sq6emm/SR6LB/3dprints/beacon-10ghz-case-mount.FCStd

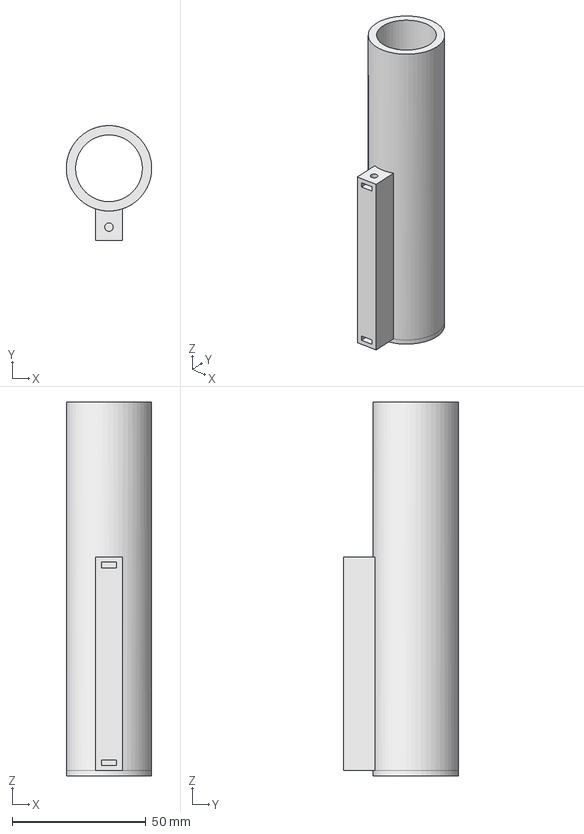
[picture p13: CAD file, 2025-03-09]
3dprints/beacon-10ghz-case-mount.FCStd
32.0 x 43.0 x 140.0 mm
