sq6emm/SR6LB/3dprints/beacon-case.FCStd

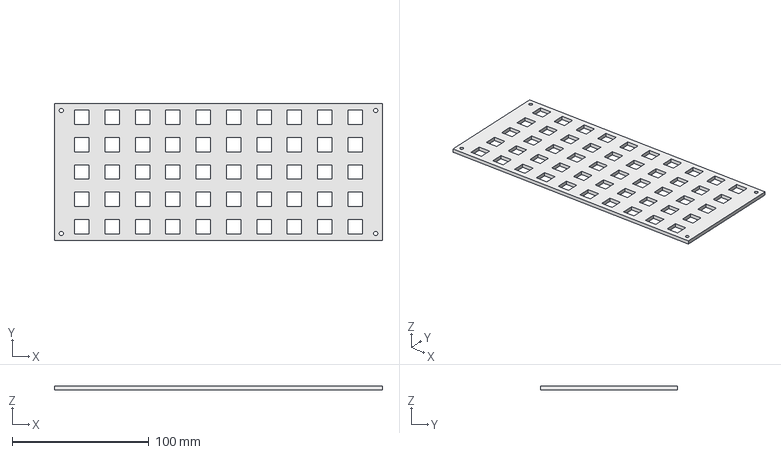
[picture p14: CAD file, 2025-03-09]
3dprints/beacon-case.FCStd
240.0 x 100.0 x 3.00 mm
